Agent-Bid/SIH_2026/pulse_ctrl.v

// Pulse controller: after a start, active is high for len clocks. Start is ignored while active.
module pulse_ctrl (
    input  wire        clk,
    input  wire        rst,
    input  wire        start,
    input  wire [23:0] len,
    output reg         active
);

    reg [23:0] count;

    always @(posedge clk)
        if (rst) begin
            active <= 1'b0;
            count  <= 24'd0;
        end
        else if (start && !active) begin
            active <= 1'b1;
            count  <= 24'd0;
        end
        else if (active) begin
            if (count == len - 1)
                active <= 1'b0;
            count <= count + 1;
        end

endmodule
