Agent-Bid/SIH_2026/sim/chirp_tb.v

`timescale 1ns/1ps
// Two windowed LFM chirps: 3 -> 7 MHz, then 7 -> 3 MHz (negative step), 16000 ticks each.
// ftw_step is FTW per clock x 2^16. Logs every tick.
// Check with: python3 host/check_chirp.py
module chirp_tb;

    localparam [23:0] LEN      = 24'd16000;      // ~320 us
    localparam [31:0] WIN_STEP = 32'd268435;     // 2^32 / 16000
    localparam [31:0] F3MHZ    = 32'd256963855;
    localparam [31:0] F7MHZ    = 32'd599582329;
    localparam [31:0] STEP     = 32'd1403365269; // (F7MHZ - F3MHZ) / LEN x 2^16

    reg                clk = 0;
    reg                rst = 1;
    reg                start = 0;
    reg         [31:0] ftw_start = F3MHZ;
    reg         [31:0] ftw_step  = STEP;
    reg         [12:0] amp = 13'd4096;
    wire signed [11:0] out;
    wire               active;

    pulse_dds dut (.clk(clk), .rst(rst), .start(start), .len(LEN),
                   .ftw_start(ftw_start), .ftw_step(ftw_step), .geo(1'b0),
                   .code(16'd0), .chip_len(16'd1),
                   .win_step(WIN_STEP), .amp(amp), .out(out), .active(active));

    always #10 clk = ~clk;

    integer fd;

    task tick(input s);
        begin
            start = s;
            @(negedge clk);
            $fdisplay(fd, "%0d %0d %0d %0d %0d %0d %0d %0d", s, ftw_start, ftw_step, amp, 0, 1, out, active);
        end
    endtask

    initial begin
        $dumpfile("sim/out/chirp_tb.vcd");
        $dumpvars(0, chirp_tb);
        fd = $fopen("sim/out/chirp_samples.txt", "w");
        $fdisplay(fd, "# len=%0d win_step=%0d", LEN, WIN_STEP);

        repeat (10) @(negedge clk);             // long enough to fill the pipeline with zeros
        rst = 0;

        repeat (50) tick(0);
        tick(1);                          // up-chirp
        repeat (16200) tick(0);

        ftw_start = F7MHZ;
        ftw_step  = -STEP;                // down-chirp
        tick(1);
        repeat (16200) tick(0);

        $fclose(fd);
        $display("wrote sim/out/chirp_samples.txt -- now run: python3 host/check_chirp.py");
        $finish;
    end

endmodule
